trevorhoner/HexDesk/STLs/connectors/double.STL

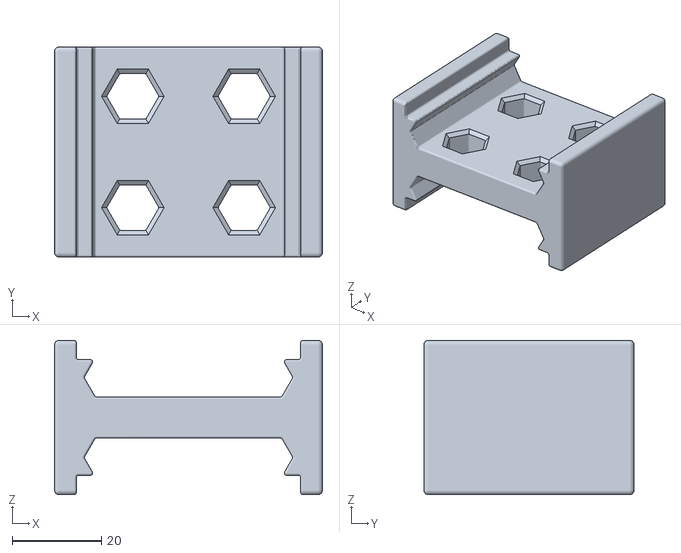
[picture p12: CAD file, 2026-08-25]
STLs/connectors/double.STL
60.2 x 47.2 x 34.7
