trevorhoner/HexDesk/STLs/hex-pin/hex-pin-15mm.STL

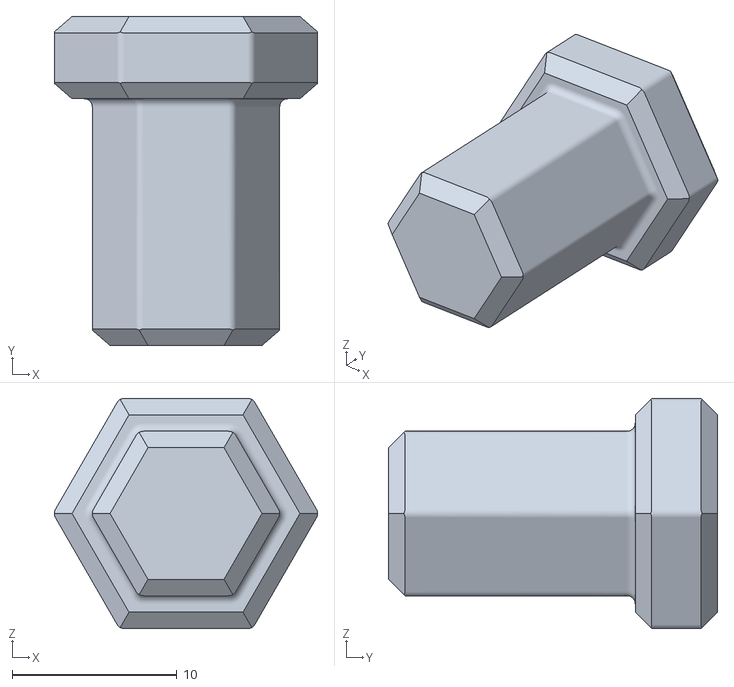
[picture p13: CAD file, 2026-08-25]
STLs/hex-pin/hex-pin-15mm.STL
16.0 x 20.0 x 14.0
