trevorhoner/HexDesk/STLs/I-bracket/2x6 (I - 0.35mm).STL

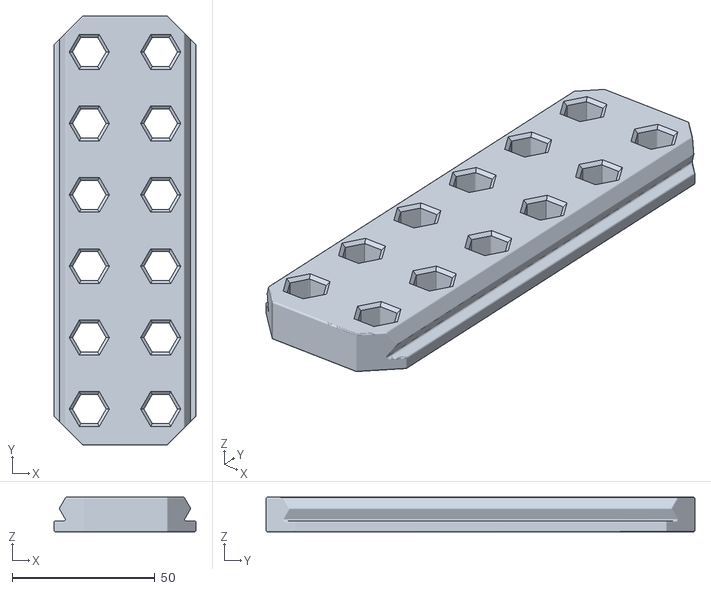
[picture p14: CAD file, 2026-08-25]
STLs/I-bracket/2x6 (I - 0.35mm).STL
49.6 x 150.2 x 12.1
