trevorhoner/HexDesk/STLs/L-bracket/2x7 (L - 0.35mm, 2H).STL

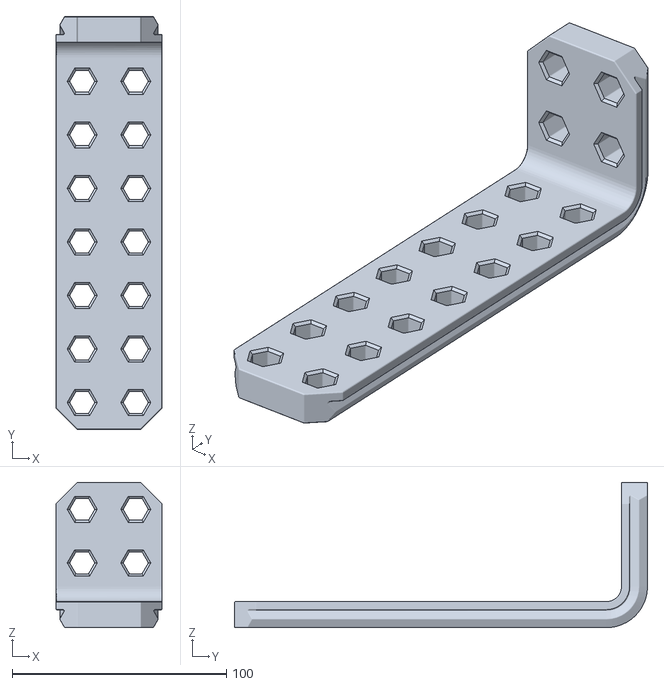
[picture p15: CAD file, 2026-08-25]
STLs/L-bracket/2x7 (L - 0.35mm, 2H).STL
49.6 x 192.8 x 67.8
