trevorhoner/HexDesk/STLs/monitor-bracket.STL

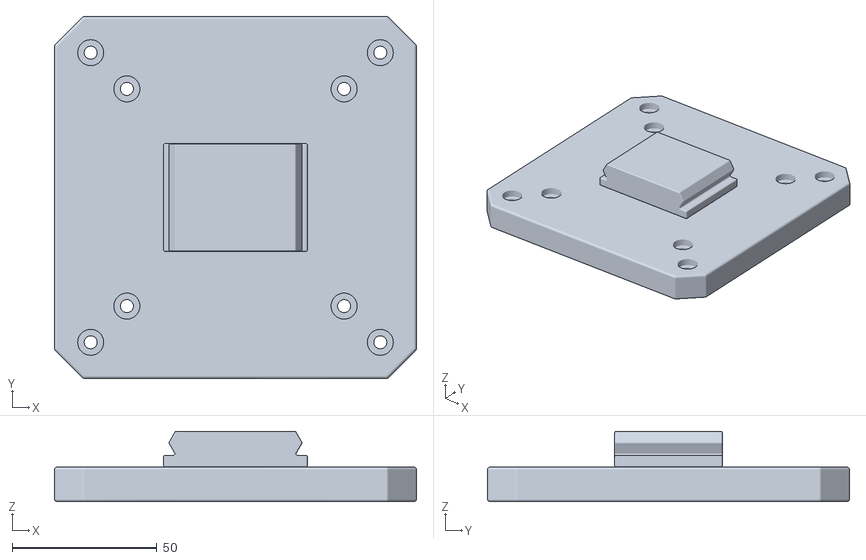
[picture p16: CAD file, 2026-08-25]
STLs/monitor-bracket.STL
125.0 x 125.0 x 24.3
