trevorhoner/HexDesk/STLs/shelf-plate/ambidextrous (flat, 125mm, 0.35mm).STL

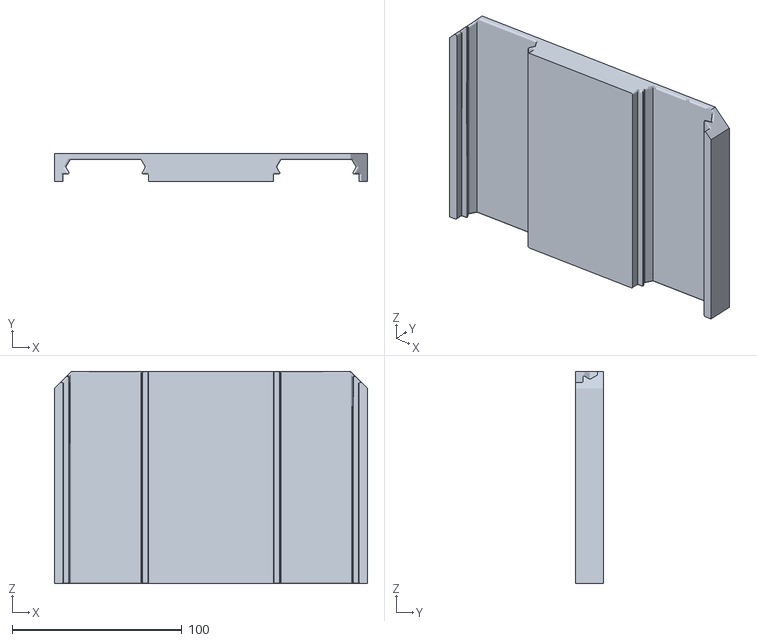
[picture p17: CAD file, 2026-09-22]
STLs/shelf-plate/ambidextrous (flat, 125mm, 0.35mm).STL
184.7 x 16.5 x 125.2
