trevorhoner/HexDesk/STLs/connectors/chamfered-single.STL

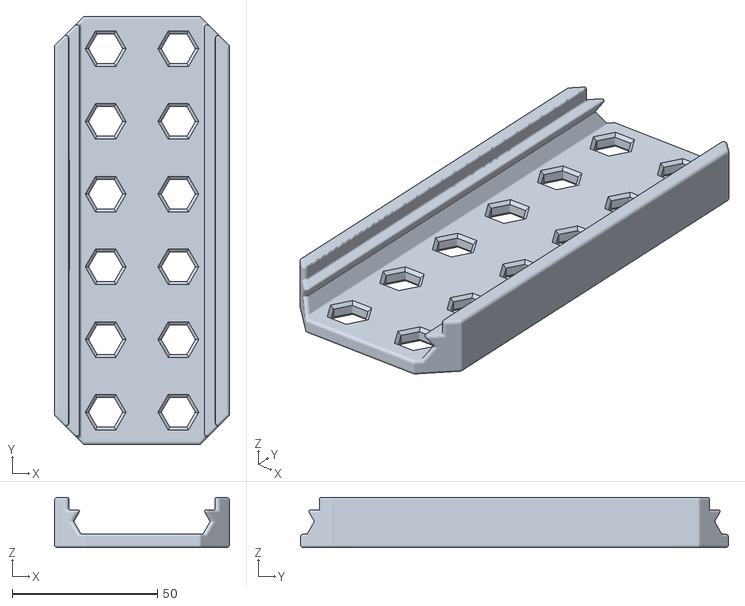
[picture p18: CAD file, 2026-08-25]
STLs/connectors/chamfered-single.STL
60.2 x 147.2 x 17.3
