trevorhoner/HexDesk/STLs/hex-pin/hex-pin-40mm.STL

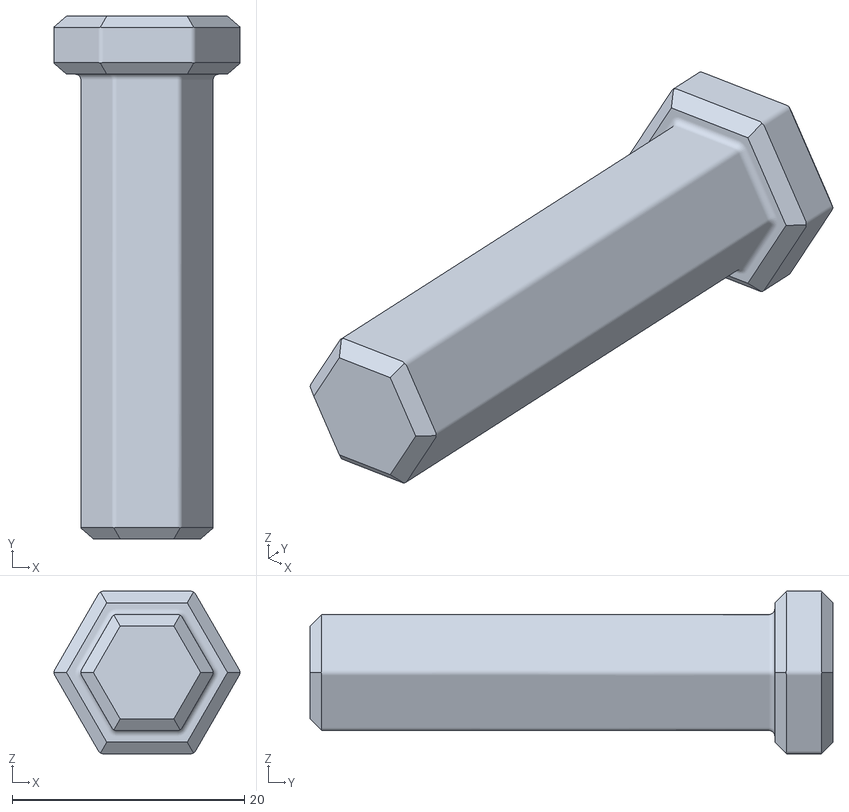
[picture p19: CAD file, 2026-08-25]
STLs/hex-pin/hex-pin-40mm.STL
16.0 x 45.0 x 14.0
