trevorhoner/HexDesk/STLs/I-bracket/2x7 (I - 0.35mm).STL

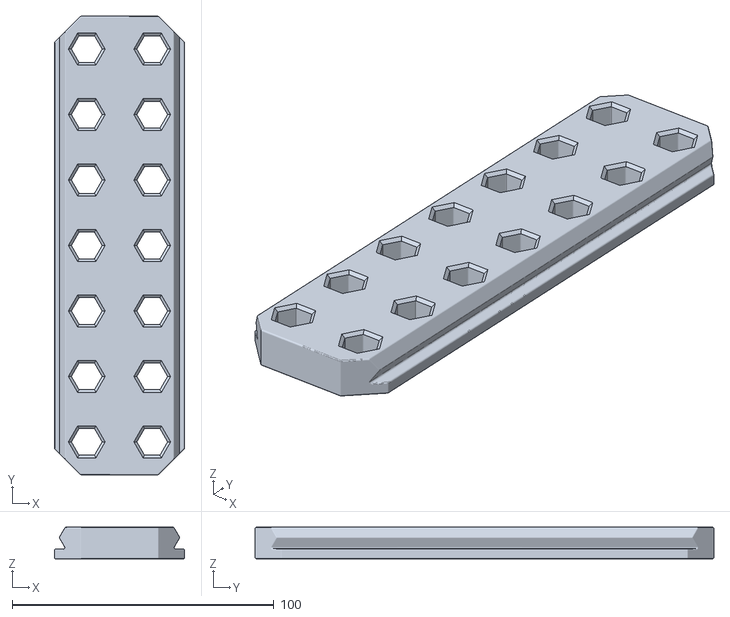
[picture p20: CAD file, 2026-08-25]
STLs/I-bracket/2x7 (I - 0.35mm).STL
49.6 x 175.2 x 12.1
