trevorhoner/HexDesk/STLs/S-bracket/3x3x3 (S - 0.35mm, 2H).STL

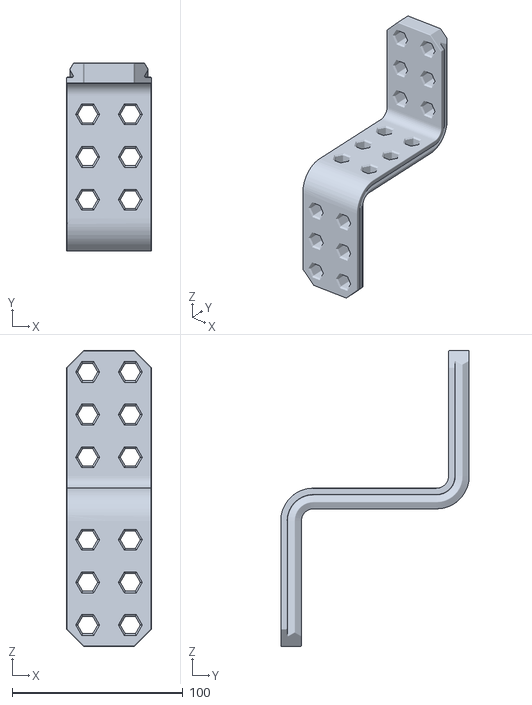
[picture p21: CAD file, 2026-08-25]
STLs/S-bracket/3x3x3 (S - 0.35mm, 2H).STL
49.6 x 110.5 x 173.5
