trevorhoner/HexDesk/STLs/hex-pin/hex-pin-30mm.STL

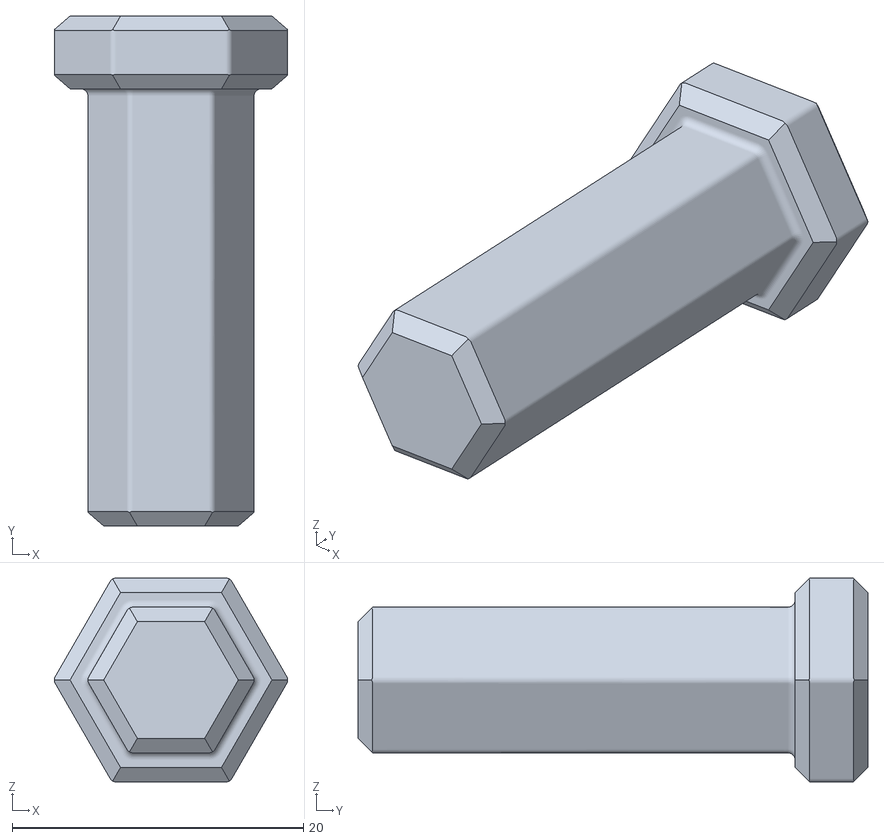
[picture p23: CAD file, 2026-08-25]
STLs/hex-pin/hex-pin-30mm.STL
16.0 x 35.0 x 14.0
