trevorhoner/HexDesk/STLs/shelf-plate/ambidextrous (brick-board, 125mm, 0.35mm).STL

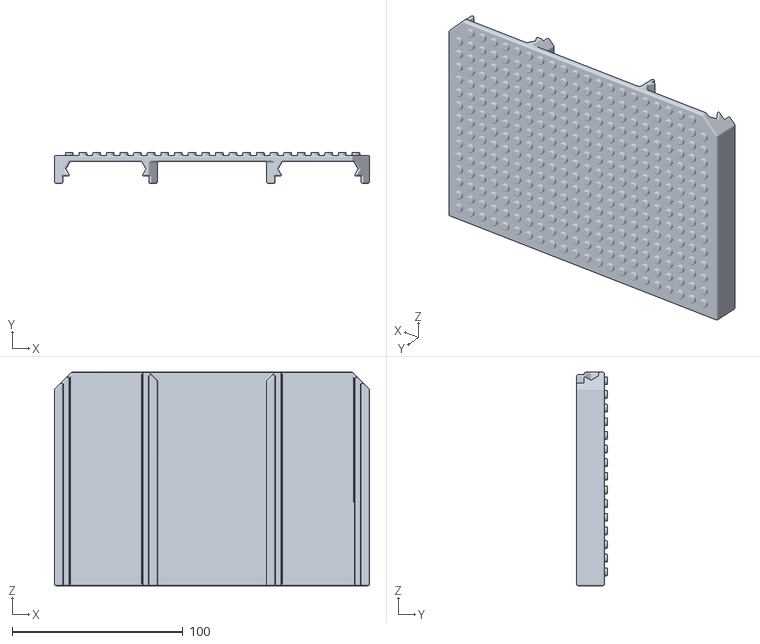
[picture p24: CAD file, 2026-09-22]
STLs/shelf-plate/ambidextrous (brick-board, 125mm, 0.35mm).STL
184.7 x 18.2 x 125.2
