trevorhoner/HexDesk/STLs/shelf-plate/left-corner (brick-board125mm, 0.35mm).STL

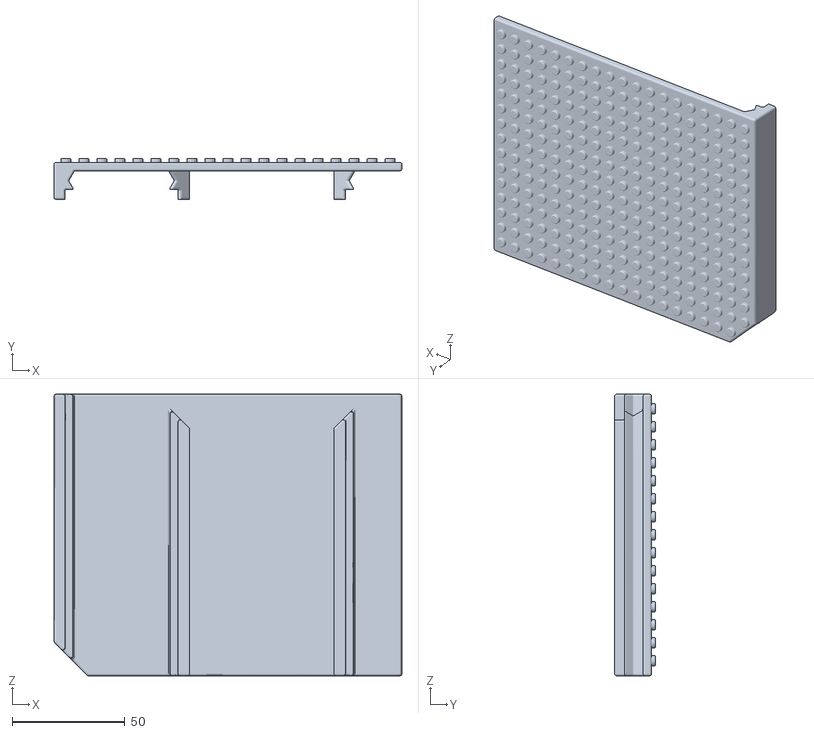
[picture p25: CAD file, 2026-08-25]
STLs/shelf-plate/left-corner (brick-board125mm, 0.35mm).STL
154.7 x 18.2 x 125.2
