trevorhoner/HexDesk/STLs/shelf-plate/left-corner (flat, 125mm, 0.35mm).STL

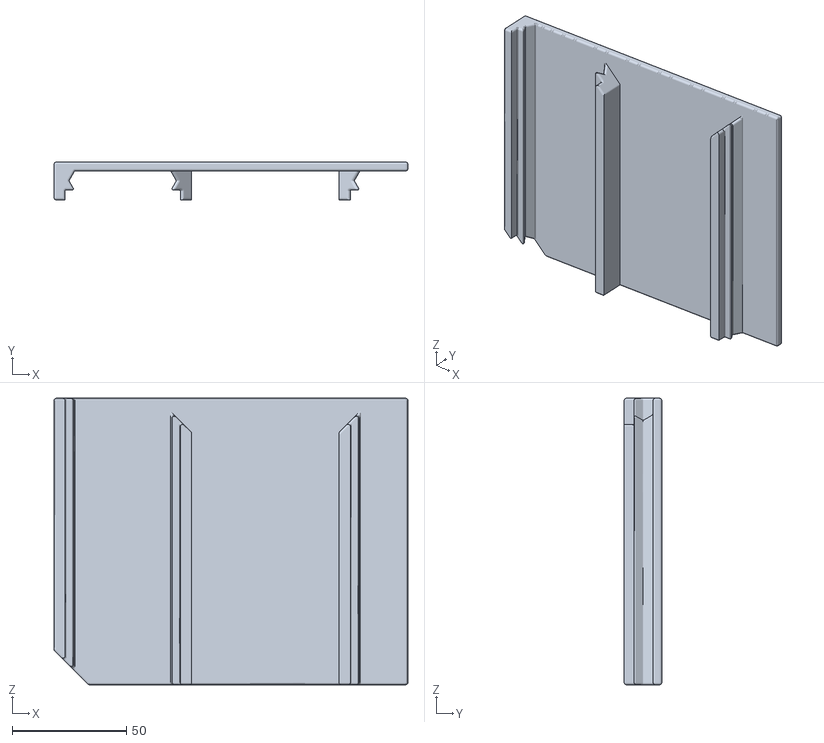
[picture p26: CAD file, 2026-08-25]
STLs/shelf-plate/left-corner (flat, 125mm, 0.35mm).STL
154.7 x 16.5 x 125.2
