trevorhoner/HexDesk/STLs/shelf-plate/right-corner (hex-holes 125mm, 0.35mm).STL

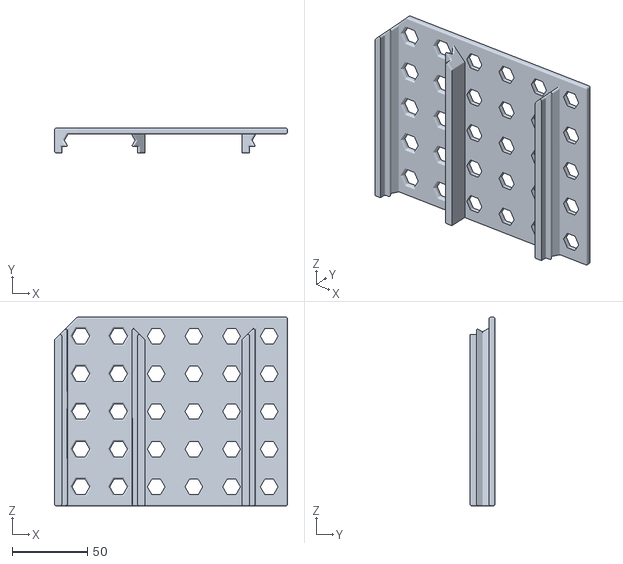
[picture p28: CAD file, 2026-08-25]
STLs/shelf-plate/right-corner (hex-holes 125mm, 0.35mm).STL
154.7 x 16.5 x 125.2
